sachleen/Smart-Parking/Arduino/Base/SIMCommunication.h

#ifndef SIMCommunication_h
#define SIMCommunication_h

#include "Arduino.h"
#include "globals.h"

class SIMCommunication
{
  public:
    SIMCommunication(unsigned long, uint8_t);
    
    // Power Functions
    void togglePower();
    void restartModule();
    bool isOn();
    
    // Send AT Commands
    String sendCommand(String, int);
    bool fancySend(String, uint8_t, int, uint8_t, ...);
    
    // Network & HTTP Communication
    bool connectToNetwork();
    String POSTRequest(String);
  private:
    uint8_t _powerPin;
    unsigned long _baud;
    
    bool responseTimedOut(int);
};

#endif
